SP5GW/Radio_Shack_Digital_Clock_Controller/doc/Digital_Clock_Controller (2).kicad_sch

## KiCad design doc/Digital_Clock_Controller (2).kicad_sch (2024-11-16)

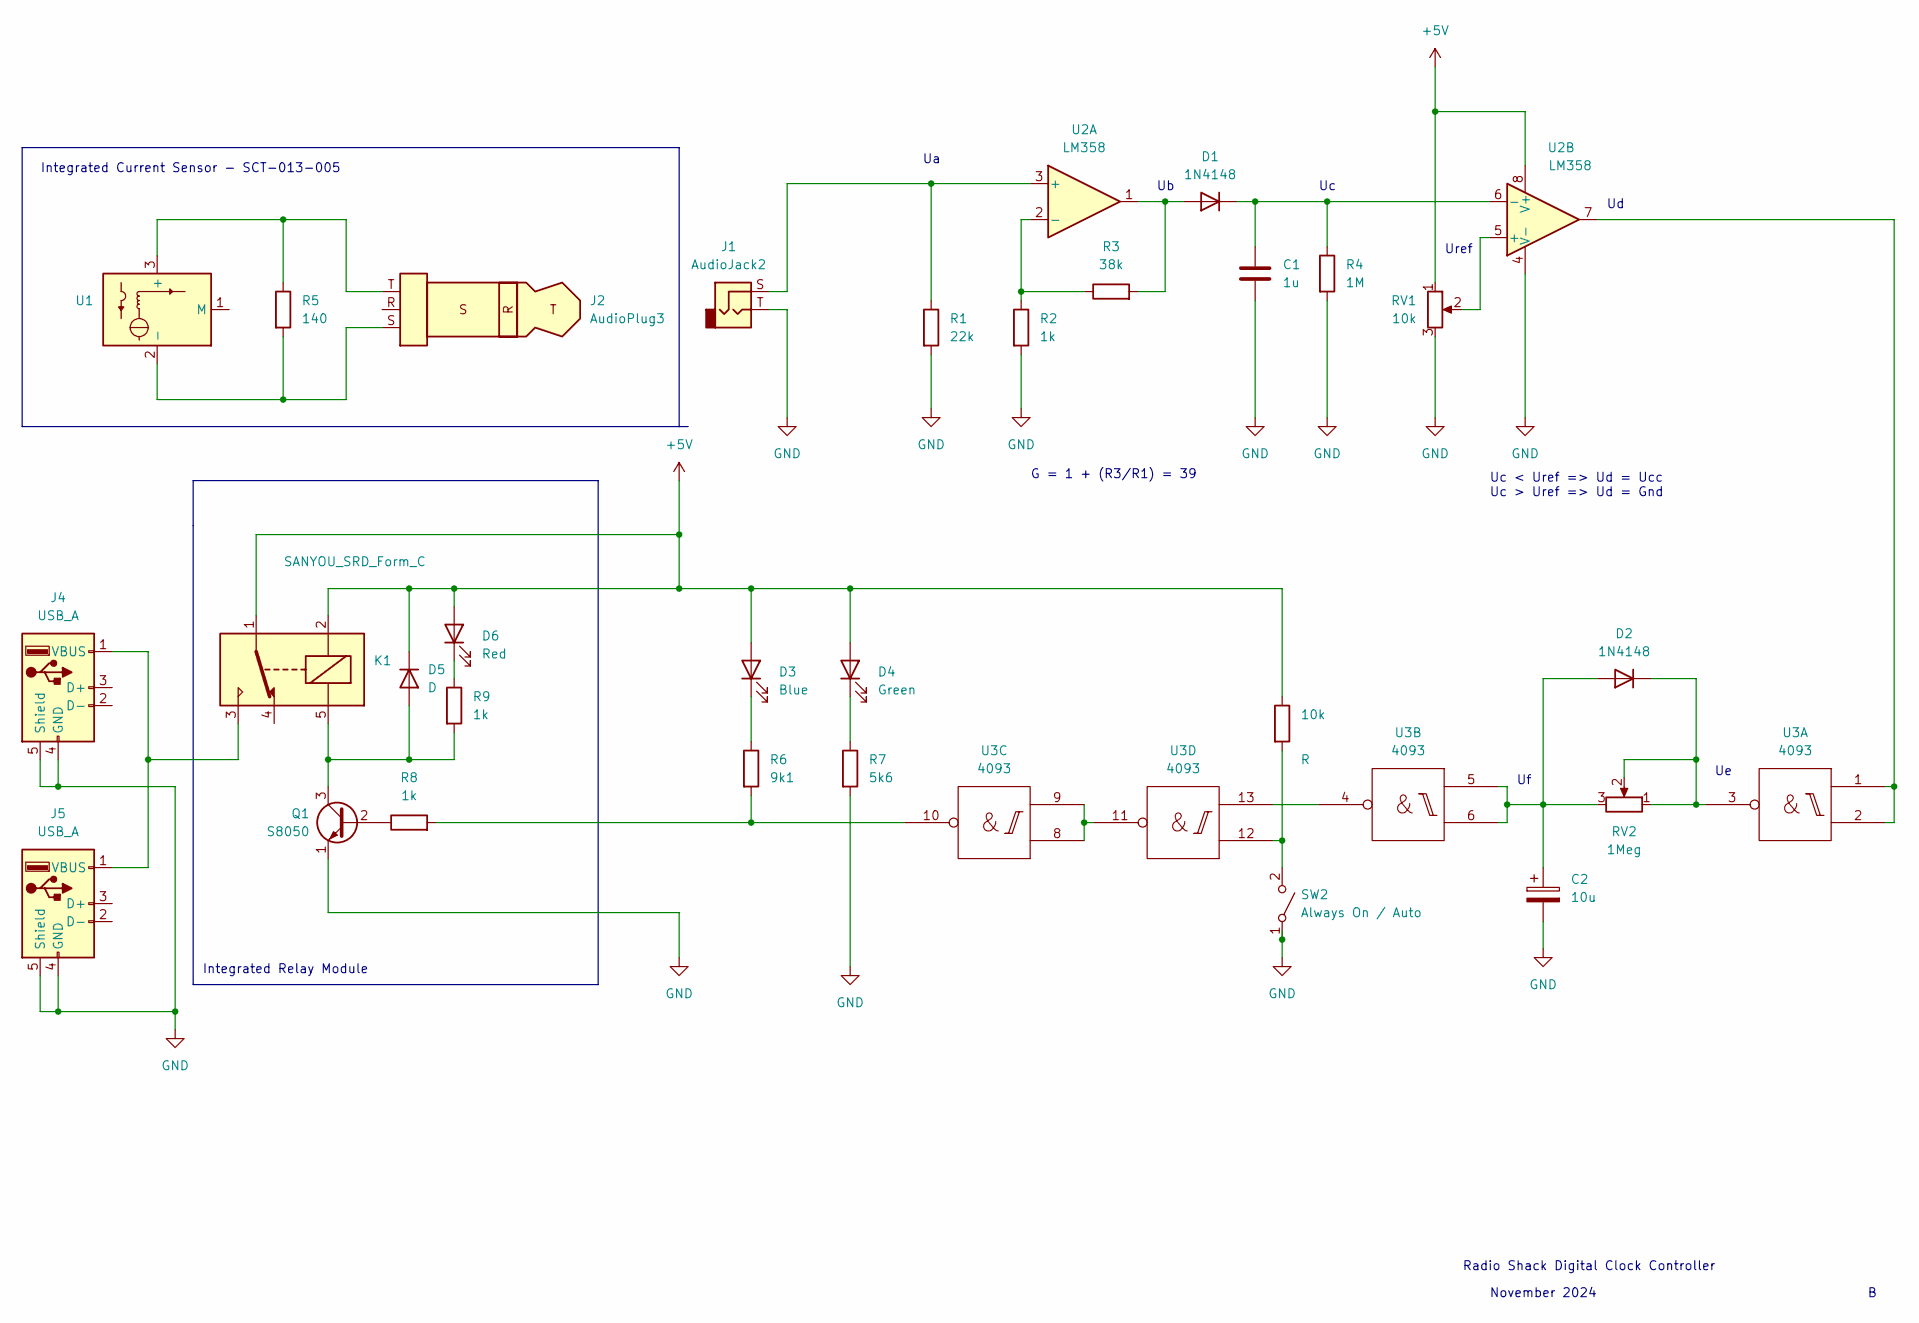
[picture p11: schematic Digital_Clock_Controller (2).kicad_sch]

Parts:
10k: R
C1: 1u
C2: 10u
D1, D2: 1N4148
D3: Blue
D4: Green
D5: D
D6: Red
J1: AudioJack2
J2: AudioPlug3
J4, J5: USB_A
K1: SANYOU_SRD_Form_C; Relay_SPDT_SANYOU_SRD_Series_Form_C
Q1: S8050; TO-92_Inline
R1: 22k
R2, R8, R9: 1k
R3: 38k
R4: 1M
R5: 140
R6: 9k1
R7: 5k6
RV1: 10k
RV2: 1Meg
SW2: Always On / Auto
U1: SCT-013-005; LEM_LA25-P
U2: LM358
U3: 4093

Connections:
+5V: 10k.1, D3.2 (A), D4.2 (A), D5.1 (K), D6.2 (A), K1.1, K1.2, RV1.1, U2.8 (V+)
GND: C1.2, C2.2, J1.T, J4.4 (GND), J4.5 (Shield), J5.4 (GND), J5.5 (Shield), Q1.1 (E), R1.2, R2.2, R4.2, R7.2, RV1.3, SW2.1 (A), U2.4 (V-)
unnamed: 10k.2, SW2.2 (B), U3.12
unnamed: C1.1, D1.1 (K), R4.1, U2.6 (-)
unnamed: C2.1, D2.2 (A), RV2.3, U3.5, U3.6
unnamed: D1.2 (A), R3.2, U2.1
unnamed: D2.1 (K), RV2.1, RV2.2, U3.3
unnamed: D3.1 (K), R6.1
unnamed: D4.1 (K), R7.1
unnamed: D5.2 (A), K1.5, Q1.3 (C), R9.2
unnamed: D6.1 (K), R9.1
unnamed: J1.S, R1.1, U2.3 (+)
unnamed: J2.S, R5.2, U1.2 (-)
unnamed: J2.T, R5.1, U1.3 (+)
unnamed: J4.1 (VBUS), J5.1 (VBUS), K1.3
unnamed: Q1.2 (B), R8.1
unnamed: R2.1, R3.1, U2.2 (-)
unnamed: R6.2, R8.2, U3.10
unnamed: RV1.2, U2.5 (+)
unnamed: U2.7, U3.1, U3.2
unnamed: U3.8, U3.9, U3.11
unnamed: U3.4, U3.13

Notes on the sheet:
Integrated Current Sensor - SCT-013-005
Uref
Radio Shack Digital Clock Controller
G = 1 + (R3/R1) = 39
Integrated Relay Module
November 2024
Uc < Uref => Ud = Ucc Uc > Uref => Ud = Gnd
